DanNixon/pi-pico-dual-ethernet/pcb/pi-pico-dual-ethernet.kicad_sch

## KiCad design pcb/pi-pico-dual-ethernet.kicad_sch (2026-02-25)

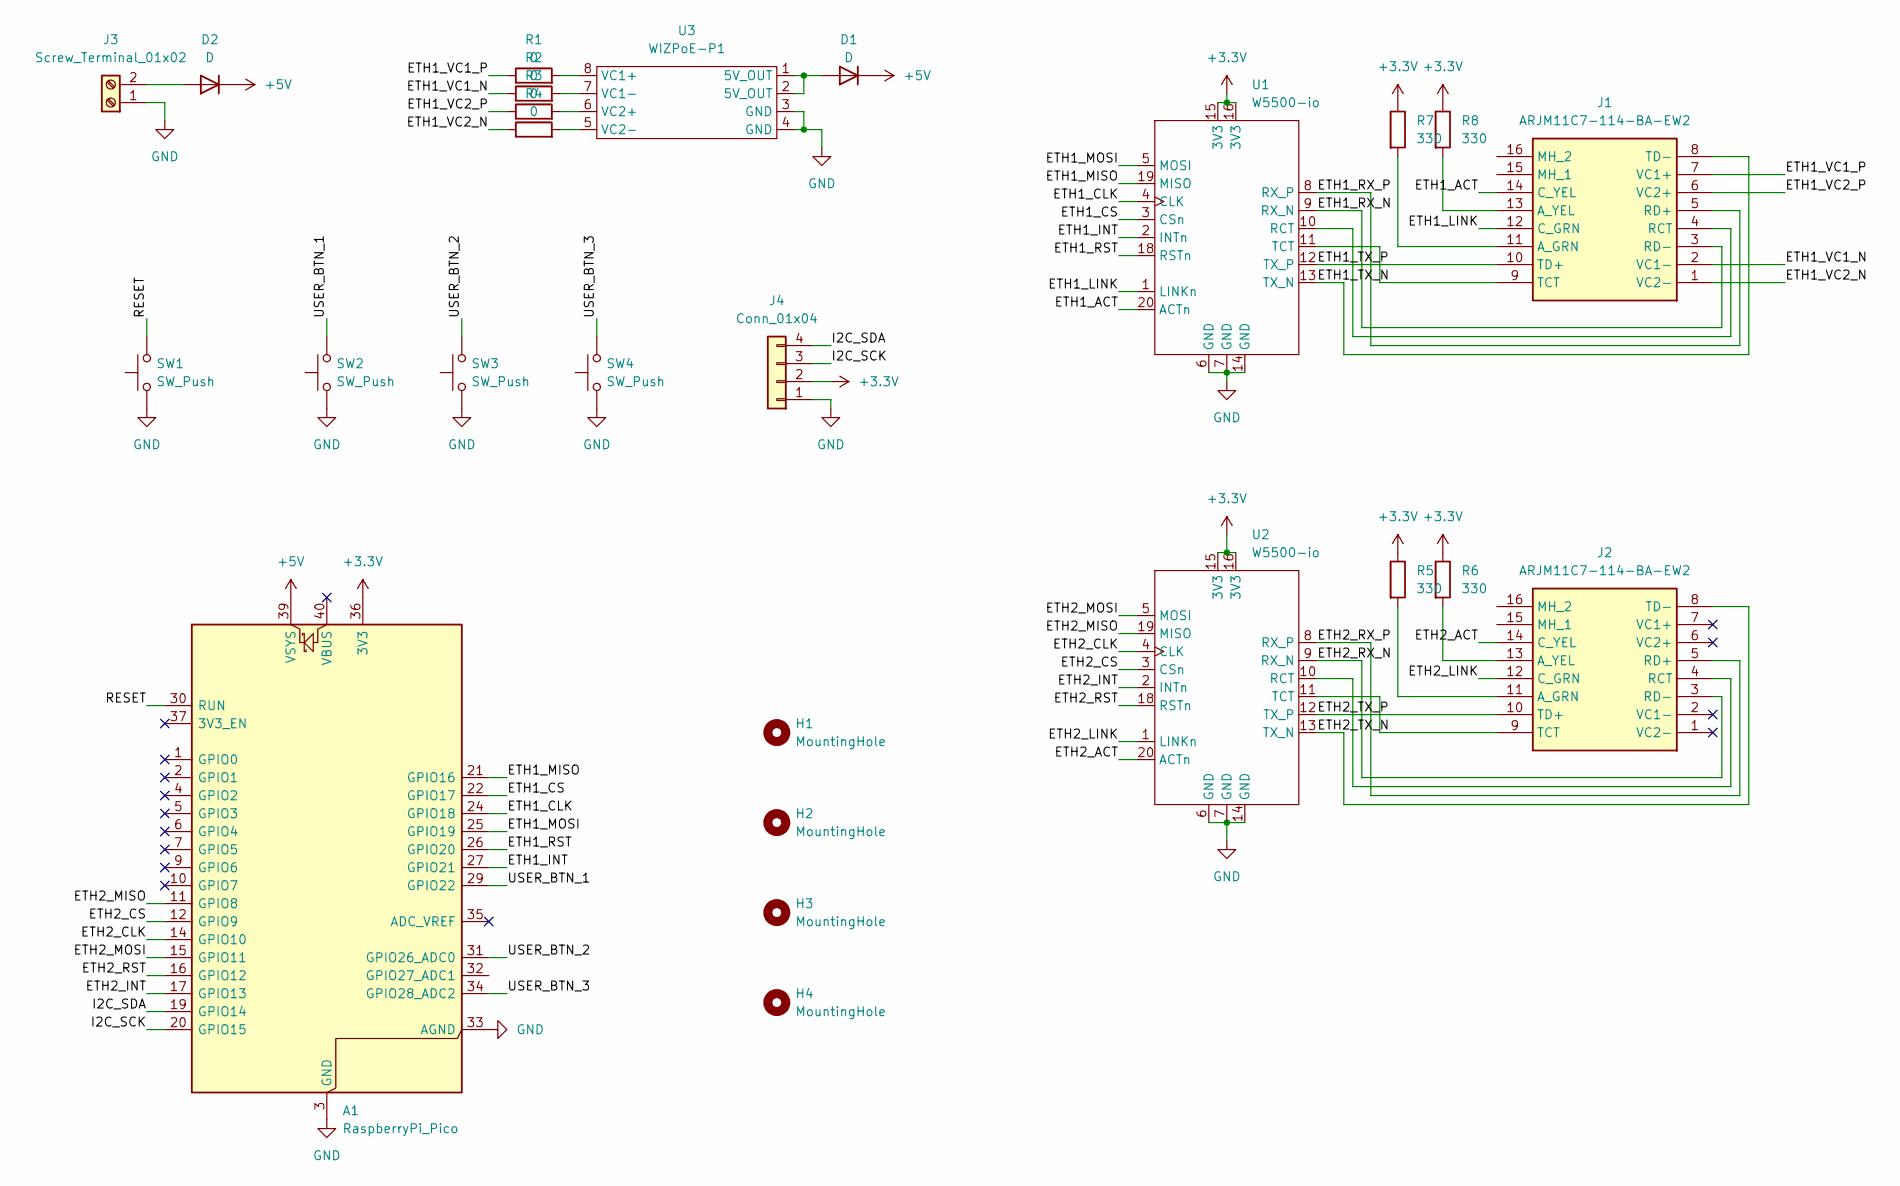
[picture p3: schematic pi-pico-dual-ethernet.kicad_sch]

Parts:
A1: RaspberryPi_Pico; RaspberryPi_Pico_Common_THT
D1, D2: D; D_SOD-123
H1, H2, H3, H4: MountingHole; MountingHole_3.2mm_M3
J1, J2: ARJM11C7-114-BA-EW2; ARJM11C7114BAEW2; Mouser Part Number 815-RJM11C7114BAEW2
J3: Screw_Terminal_01x02; CTB7000-2
J4: Conn_01x04; PinSocket_1x04_P2.54mm_Vertical
R1, R2, R3, R4: 0; R_1206_3216Metric_Pad1.30x1.75mm_HandSolder
R5, R6, R7, R8: 330; R_1206_3216Metric_Pad1.30x1.75mm_HandSolder
SW1, SW2, SW3, SW4: SW_Push; SW_PUSH_6mm
U1, U2: W5500-io
U3: WIZPoE-P1

Connections:
+3.3V: A1.36 (3V3), J4.2, R5.1, R6.1, R7.1, R8.1, U1.15 (3V3), U1.16 (3V3), U2.15 (3V3), U2.16 (3V3)
+5V: A1.39 (VSYS), D1.1 (K), D2.1 (K)
ETH1_ACT: J1.14 (C_YEL), U1.20 (ACTn)
ETH1_CLK: A1.24 (GPIO18), U1.4 (CLK)
ETH1_CS: A1.22 (GPIO17), U1.3 (CSn)
ETH1_INT: A1.27 (GPIO21), U1.2 (INTn)
ETH1_LINK: J1.12 (C_GRN), U1.1 (LINKn)
ETH1_MISO: A1.21 (GPIO16), U1.19 (MISO)
ETH1_MOSI: A1.25 (GPIO19), U1.5 (MOSI)
ETH1_RST: A1.26 (GPIO20), U1.18 (RSTn)
ETH1_RX_N: J1.3 (RD-), U1.9 (RX_N)
ETH1_RX_P: J1.5 (RD+), U1.8 (RX_P)
ETH1_TX_N: J1.8 (TD-), U1.13 (TX_N)
ETH1_TX_P: J1.10 (TD+), U1.12 (TX_P)
ETH1_VC1_N: J1.2 (VC1-), R2.1
ETH1_VC1_P: J1.7 (VC1+), R1.1
ETH1_VC2_N: J1.1 (VC2-), R4.1
ETH1_VC2_P: J1.6 (VC2+), R3.1
ETH2_ACT: J2.14 (C_YEL), U2.20 (ACTn)
ETH2_CLK: A1.14 (GPIO10), U2.4 (CLK)
ETH2_CS: A1.12 (GPIO9), U2.3 (CSn)
ETH2_INT: A1.17 (GPIO13), U2.2 (INTn)
ETH2_LINK: J2.12 (C_GRN), U2.1 (LINKn)
ETH2_MISO: A1.11 (GPIO8), U2.19 (MISO)
ETH2_MOSI: A1.15 (GPIO11), U2.5 (MOSI)
ETH2_RST: A1.16 (GPIO12), U2.18 (RSTn)
ETH2_RX_N: J2.3 (RD-), U2.9 (RX_N)
ETH2_RX_P: J2.5 (RD+), U2.8 (RX_P)
ETH2_TX_N: J2.8 (TD-), U2.13 (TX_N)
ETH2_TX_P: J2.10 (TD+), U2.12 (TX_P)
GND: A1.3 (GND), A1.8 (GND), A1.13 (GND), A1.18 (GND), A1.23 (GND), A1.28 (GND), A1.33 (AGND), A1.38 (GND), J3.1, J4.1, SW1.1, SW2.1, SW3.1, SW4.1, U1.6 (GND), U1.7 (GND), U1.14 (GND), U2.6 (GND), U2.7 (GND), U2.14 (GND), U3.3 (GND), U3.4 (GND)
I2C_SCK: A1.20 (GPIO15), J4.3
I2C_SDA: A1.19 (GPIO14), J4.4
unnamed: D1.2 (A), U3.1 (5V_OUT), U3.2 (5V_OUT)
unnamed: D2.2 (A), J3.2
unnamed: J1.4 (RCT), U1.10 (RCT)
unnamed: J1.9 (TCT), U1.11 (TCT)
unnamed: J1.11 (A_GRN), R7.2
unnamed: J1.13 (A_YEL), R8.2
unnamed: J2.4 (RCT), U2.10 (RCT)
unnamed: J2.9 (TCT), U2.11 (TCT)
unnamed: J2.11 (A_GRN), R5.2
unnamed: J2.13 (A_YEL), R6.2
unnamed: R1.2, U3.8 (VC1+)
unnamed: R2.2, U3.7 (VC1-)
unnamed: R3.2, U3.6 (VC2+)
unnamed: R4.2, U3.5 (VC2-)
RESET: A1.30 (RUN), SW1.2
USER_BTN_1: A1.29 (GPIO22), SW2.2
USER_BTN_2: A1.31 (GPIO26_ADC0), SW3.2
USER_BTN_3: A1.34 (GPIO28_ADC2), SW4.2
